thesunRider/Pragview/code/esp/main/ESP32OTAPull.h

/*
ESP32-OTA-Pull - a library for doing "pull" based OTA ("Over The Air") firmware
updates, where the image updates are posted on the web.

MIT License

Copyright (c) 2022-3 Mikal Hart

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
THE SOFTWARE IS PROVIDED "AS IS", WITHOUT WARRANTY OF ANY KIND, EXPRESS OR
IMPLIED, INCLUDING BUT NOT LIMITED TO THE WARRANTIES OF MERCHANTABILITY,
FITNESS FOR A PARTICULAR PURPOSE AND NONINFRINGEMENT. IN NO EVENT SHALL THE
AUTHORS OR COPYRIGHT HOLDERS BE LIABLE FOR ANY CLAIM, DAMAGES OR OTHER
LIABILITY, WHETHER IN AN ACTION OF CONTRACT, TORT OR OTHERWISE, ARISING FROM,
OUT OF OR IN CONNECTION WITH THE SOFTWARE OR THE USE OR OTHER DEALINGS IN THE
SOFTWARE.
*/

#pragma once
#include <HTTPClient.h>
#include <ArduinoJson.h>
#include <Update.h>
#include <WiFi.h>
#include <WiFiClientSecure.h>

class ESP32OTAPull {
public:
  struct HttpResult {
    int responseCode;
    size_t contentLength;
  };
  enum ActionType { DONT_DO_UPDATE,
                    UPDATE_BUT_NO_BOOT,
                    UPDATE_AND_BOOT };

  // Return codes from CheckForOTAUpdate
  enum ErrorCode { UPDATE_AVAILABLE = -3,
                   NO_UPDATE_PROFILE_FOUND = -2,
                   NO_UPDATE_AVAILABLE = -1,
                   UPDATE_OK = 0,
                   HTTP_FAILED = 1,
                   WRITE_ERROR = 2,
                   JSON_PROBLEM = 3,
                   OTA_UPDATE_FAIL = 4 };

private:
  void (*Callback)(int offset, int totallength) = NULL;
  ActionType Action = UPDATE_AND_BOOT;
  String Board = ARDUINO_BOARD;
  String Device = "";
  String Config = "";
  String CVersion = "";
  bool DowngradesAllowed = false;
  bool SerialDebug = false;
  WiFiClientSecure *client;

  HttpResult followRedirects(WiFiClientSecure *client, String url, int maxRedirects) {
   client->flush();
   client->stop();
    HttpResult result = { 0, 0 };

    for (int i = 0; i < maxRedirects; i++) {
      String host, path;
      int port;
      if (!parseURL(url, host, path, port)) {
        Serial.println("Invalid URL: " + url);
        result.responseCode = -1;
        return result;
      }

      Serial.println("Connecting to: " + host);
      if (!client->connect(host.c_str(), port)) {
        Serial.println("Connection failed");
        result.responseCode = -2;
        return result;
      }

      // Send request
      client->print(String("GET ") + path + " HTTP/1.1\r\n" + "Host: " + host + "\r\n" + "User-Agent: ESP32\r\n" + "Connection: close\r\n\r\n");

      // Read status line
      String statusLine = client->readStringUntil('\n');
      Serial.println(statusLine);
      int statusCode = parseStatusCode(statusLine);

      // Read headers
      String location = "";
      size_t contentLength = 0;
      while (true) {
        String line = client->readStringUntil('\n');
        if (line == "\r") break;  // End of headers
        Serial.println(line);
        if (line.startsWith("Location: ")) {
          location = line.substring(10);
          location.trim();
        }
        if (line.startsWith("Content-Length: ")) {
          contentLength = line.substring(16).toInt();
        }
      }

      // If redirect, follow new URL
      if (statusCode >= 300 && statusCode < 400 && location.length() > 0) {
        Serial.println("Redirecting to: " + location);
        url = location;
        client->stop();
        continue;
      }

      // Final response
      result.responseCode = statusCode;
      result.contentLength = contentLength;

      // Print body (stream)
      Serial.println("Fin main :");

      break;
    }

    return result;
  }


  bool parseURL(const String &url, String &host, String &path, int &port) {
    if (!url.startsWith("http")) return false;
    int schemeEnd = url.indexOf("://");
    int pathStart = url.indexOf('/', schemeEnd + 3);
    host = url.substring(schemeEnd + 3, pathStart);
    path = url.substring(pathStart);
    port = url.startsWith("https") ? 443 : 80;
    return true;
  }

  int parseStatusCode(const String &statusLine) {
    int firstSpace = statusLine.indexOf(' ');
    int secondSpace = statusLine.indexOf(' ', firstSpace + 1);
    return statusLine.substring(firstSpace + 1, secondSpace).toInt();
  }

  int DoOTAUpdate(WiFiClientSecure *client,const char *URL, ActionType Action) {
    Serial.println("starting ota update");
    String mainURL(URL);
    Serial.print("loading new URL:");
    Serial.println(URL);
    HttpResult result = followRedirects(client, mainURL, 5);
    //Forces redirect following, enables OTA updates from more online sources, like GitHub releases.

    // Send HTTP GET request
    int httpResponseCode = result.responseCode;

    if (httpResponseCode == 200) {
      int totalLength = result.contentLength;

      // this is required to start firmware update process
      if (!Update.begin(UPDATE_SIZE_UNKNOWN))
        return OTA_UPDATE_FAIL;

      // create buffer for read
      uint8_t buff[1280] = { 0 };

      // get tcp stream
      WiFiClient *stream = client;

      // read all data from server
      int offset = 0;
      while (offset < totalLength) {
        size_t sizeAvail = stream->available();
        if (sizeAvail > 0) {
          size_t bytes_to_read = min(sizeAvail, sizeof(buff));
          size_t bytes_read = stream->readBytes(buff, bytes_to_read);
          size_t bytes_written = Update.write(buff, bytes_read);
          if (bytes_read != bytes_written) {
            if (SerialDebug) {
              Serial.printf("Unexpected error in OTA: %d %d %d\n", bytes_to_read, bytes_read, bytes_written);
              Serial.printf("Write returned 0? Common causes are:\n");
              Serial.printf("Using merged .bin file instead of just the app .bin from Arduino\n");
              Serial.printf("Flash encryption configuration issues.\n");
            }
            break;
          }
          offset += bytes_written;
          if (Callback != NULL)
            Callback(offset, totalLength);
        }
      }

      if (offset == totalLength) {
        Update.end(true);
        delay(1000);

        // Restart ESP32 to see changes
        if (Action == UPDATE_BUT_NO_BOOT)
          return UPDATE_OK;
        ESP.restart();
      }
      return WRITE_ERROR;
    }

    return httpResponseCode;
  }

public:
  /// @brief Return the version string of the binary, as reported by the JSON
  /// @return The firmware version
  String GetVersion() {
    return CVersion;
  }

  /// @brief Override the default "Device" id (MAC Address)
  /// @param device A string identifying the particular device (instance) (typically e.g., a MAC address)
  /// @return The current ESP32OTAPull object for chaining
  ESP32OTAPull &OverrideDevice(const char *device) {
    Device = device;
    return *this;
  }

  /// @brief Override the default "Board" value of ARDUINO_BOARD
  /// @param board A string identifying the board (class) being targeted
  /// @return The current ESP32OTAPull object for chaining
  ESP32OTAPull &OverrideBoard(const char *board) {
    Board = board;
    return *this;
  }

  /// @brief Specify a configuration string that must match any "Config" in JSON
  /// @param config An arbitrary string showing the current configuration
  /// @return The current ESP32OTAPull object for chaining
  ESP32OTAPull &SetConfig(const char *config) {
    Config = config;
    return *this;
  }

  /// @brief Specify whether downgrades (posted version is lower) are allowed
  /// @param allow_downgrades true if downgrades are allowed
  /// @return The current ESP32OTAPull object for chaining
  ESP32OTAPull &AllowDowngrades(bool allow_downgrades) {
    DowngradesAllowed = allow_downgrades;
    return *this;
  }

  /// @brief Specify a callback function to monitor update progress
  /// @param callback Pointer to a function that is called repeatedly during update
  /// @return The current ESP32OTAPull object for chaining
  ESP32OTAPull &SetCallback(void (*callback)(int offset, int totallength)) {
    Callback = callback;
    return *this;
  }

  /// @brief Enable extra debugging output on Serial if required.
  void EnableSerialDebug() {
    SerialDebug = true;
  }

  /// @brief The main entry point for OTA Update
  /// @param JSON_URL The URL for the JSON filter file
  /// @param CurrentVersion The version # of the current (i.e. to be replaced) sketch
  /// @param ActionType The action to be performed.  May be any of DONT_DO_UPDATE, UPDATE_BUT_NO_BOOT, UPDATE_AND_BOOT (default)
  /// @return ErrorCode or HTTP failure code (see enum above)
  int CheckForOTAUpdate(WiFiClientSecure *client,const char *JSON_URL, const char *CurrentVersion, ActionType Action = UPDATE_AND_BOOT) {
    CurrentVersion = CurrentVersion == NULL ? "" : CurrentVersion;

    String mainURL(JSON_URL);
    HttpResult result = followRedirects(client, mainURL, 5);

    // Send HTTP GET request
    int httpResponseCode = result.responseCode;

    if (SerialDebug) {
      Serial.print("Got HTTP Response: ");
      Serial.println(httpResponseCode, DEC);
    }

    if (httpResponseCode != 200) {
      return httpResponseCode > 0 ? httpResponseCode : HTTP_FAILED;
    }

    Serial.println("Downloading JSON...");
    String downloadedJson;
    downloadedJson.reserve(2000);

    while (client->available()) {
      downloadedJson += (char)client->read();  // append each byte
      delay(1);
    }
    client->stop();
    Serial.println();
    // Parse response
    JsonDocument doc;

    // Parse JSON object (and intercept)
    //ReadLoggingStream loggingStream(rawStream, Serial);
    //DeserializationError error = deserializeJson(doc, loggingStream);

    // Parse JSON object
    DeserializationError error = deserializeJson(doc, downloadedJson.c_str());


    if (error) {
      if (SerialDebug) {
        Serial.print(F("deserializeJson() failed: "));
        Serial.println(error.f_str());
      }
      return JSON_PROBLEM;
    }
    Serial.println(downloadedJson);
    String _Board = Board.isEmpty() ? ARDUINO_BOARD : Board;
    String _Device = Device.isEmpty() ? WiFi.macAddress() : Device;
    String _Config = Config.isEmpty() ? "" : Config;
    bool foundProfile = false;

    if (SerialDebug) {

      Serial.println("Looking for a configuration that matches:");
      Serial.print("Board: ");
      Serial.println(_Board);
      Serial.print("Version: ");
      Serial.println(CurrentVersion);
      Serial.print("Device: ");
      Serial.println(_Device);
    }

    // Step through the configurations looking for a match
    for (auto config : doc["Configurations"].as<JsonArray>()) {
      String CBoard = config["Board"].isNull() ? "" : (const char *)config["Board"];
      String CDevice = config["Device"].isNull() ? "" : (const char *)config["Device"];
      CVersion = config["Version"].isNull() ? "" : (const char *)config["Version"];
      String CConfig = config["Config"].isNull() ? "" : (const char *)config["Config"];
      Serial.println("Stepping...");

      if ((CBoard.isEmpty() || CBoard == _Board) && (CDevice.isEmpty() || CDevice == _Device) && (CConfig.isEmpty() || CConfig == _Config)) {
        if (CVersion.isEmpty() || CVersion > String(CurrentVersion) || (DowngradesAllowed && CVersion != String(CurrentVersion))) {
          Serial.println("Doing action");
          return Action == DONT_DO_UPDATE ? UPDATE_AVAILABLE : DoOTAUpdate(client,config["URL"], Action);
        }
        foundProfile = true;
      }
    }
    return foundProfile ? NO_UPDATE_AVAILABLE : NO_UPDATE_PROFILE_FOUND;
  }
};
